plan44/p44ttngw-hardware/p44ttngw-kicad/p44ttngw.sch

## KiCad design p44ttngw-kicad/p44ttngw.sch (2017-11-21)

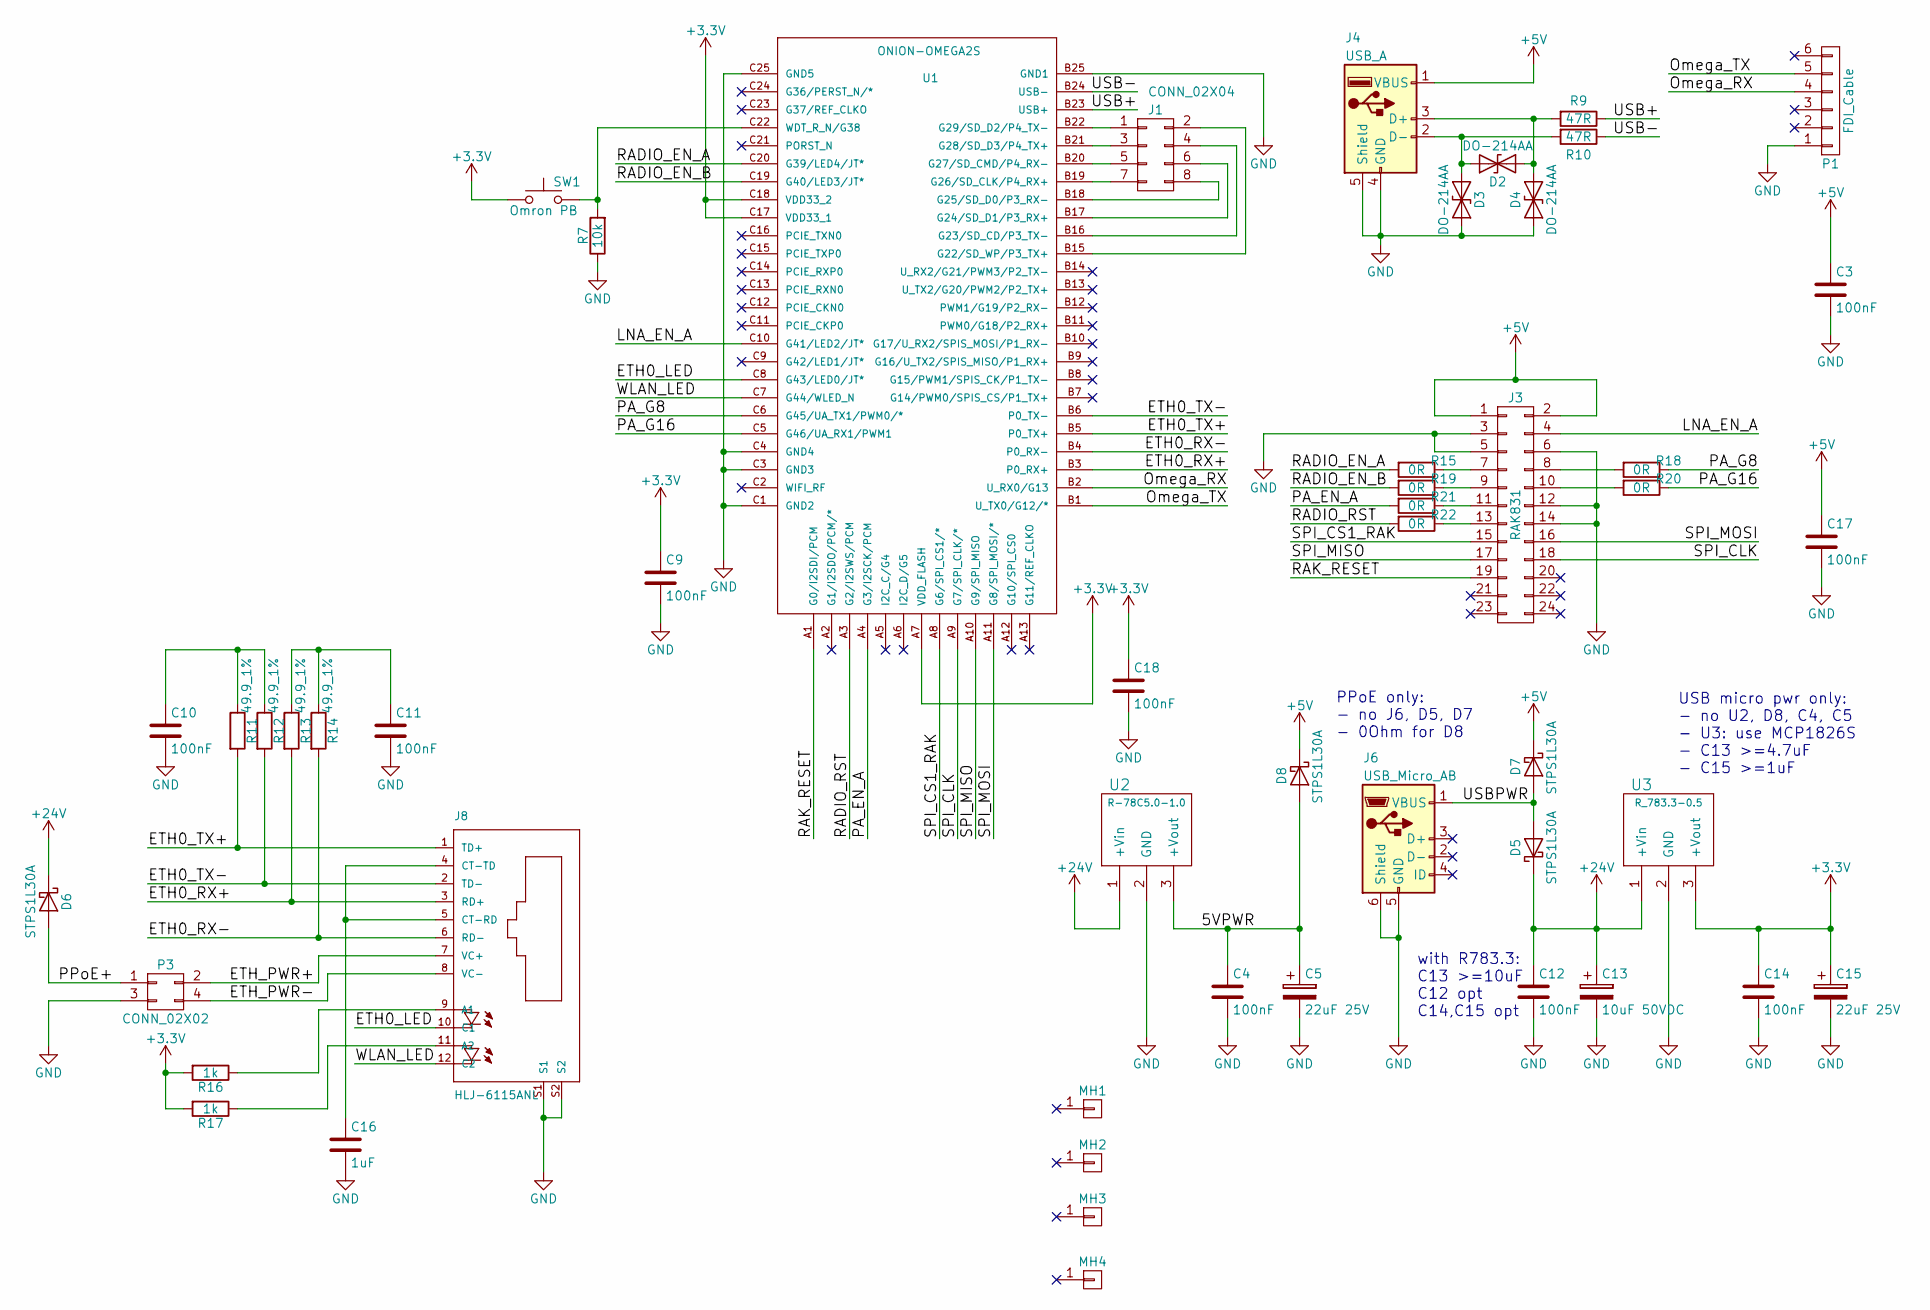
[picture p8: schematic p44ttngw.sch]

Parts:
C3, C4, C9, C10, C11, C12, C14, C17, C18: 100nF; C_1206_HandSoldering
C5, C15: 22uF 25V; CP_Radial_D7.5mm_P2.50mm
C13: 10uF 50VDC; CP_Radial_D7.5mm_P2.50mm
C16: 1uF; C_1206_HandSoldering
D2, D3, D4: DO-214AA; D_SMB_Handsoldering
D5, D6, D7, D8: STPS1L30A; D_SMA_Handsoldering
J1: CONN_02X04; Pin_Header_Straight_2x04_Pitch2.54mm
J3: RAK831
J4: USB_A
J6: USB_Micro_AB; USB_Micro-B-SMD
J8: HLJ-6115ANL
MH1, MH2, MH3, MH4: CONN_01X01; MountingHole_3.2mm_M3_DIN965_Pad
P1: FDI_Cable; Pin_Header_Straight_1x06_Pitch2.54mm
P3: CONN_02X02; Pin_Header_Straight_2x02_Pitch2.54mm
R7: 10k; R_1206_HandSoldering
R9, R10: 47R; R_1206_HandSoldering
R11, R12, R13, R14: 49.9_1%; R_0805_HandSoldering
R15, R18, R19, R20, R21, R22: 0R; R_1206_HandSoldering
R16, R17: 1k; R_1206_HandSoldering
SW1: Omron PB; SW_PUSH_6mm_h4.3mm
U1: ONION-OMEGA2S
U2: R-78C5.0-1.0; Recom-R78Cxx
U3: R_783.3-0.5; Recom-R78Cxx

Connections:
5VPWR: C4.1, C5.1, D8.2 (A), U2.3 (+Vout)
+3.3V: C9.1, C14.1, C15.1, C18.1, R16.2, R17.2, SW1.1, U1.A7 (VDD_FLASH), U1.C17 (VDD33_1), U1.C18 (VDD33_2), U3.3 (+Vout)
+5V: C3.1, C17.1, D7.1 (K), D8.1 (K), J3.1, J3.2, J4.1 (VBUS)
+24V: C12.1, C13.1, D5.1 (K), D6.1 (K), U2.1 (+Vin), U3.1 (+Vin)
ETH0_LED: J8.10 (C1), U1.C8 (G43/LED0/JT*)
ETH0_RX+: J8.3 (RD+), R13.2, U1.B3 (P0_RX+)
ETH0_RX-: J8.6 (RD-), R14.2, U1.B4 (P0_RX-)
ETH0_TX+: J8.1 (TD+), R11.2, U1.B5 (P0_TX+)
ETH0_TX-: J8.2 (TD-), R12.2, U1.B6 (P0_TX-)
ETH_PWR+: J8.7 (VC+), P3.2
ETH_PWR-: J8.8 (VC-), P3.4
GND: C3.2, C4.2, C5.2, C9.2, C10.2, C11.2, C12.2, C13.2, C14.2, C15.2, C16.2, C17.2, C18.2, D3.2 (A2), D4.2 (A2), J3.3, J3.5, J3.6, J3.12, J3.14, J4.4 (GND), J4.5 (Shield), J6.5 (GND), J6.6 (Shield), J8.S1, J8.S2, P1.1, P3.3, R7.1, U1.B25 (GND1), U1.C1 (GND2), U1.C3 (GND3), U1.C4 (GND4), U1.C25 (GND5), U2.2 (GND), U3.2 (GND)
LNA_EN_A: J3.4, U1.C10 (G41/LED2/JT*)
unnamed: C10.1, R11.1, R12.1
unnamed: C11.1, R13.1, R14.1
unnamed: C16.1, J8.4 (CT-TD), J8.5 (CT-RD)
unnamed: D2.1 (A1), D4.1 (A1), J4.3 (D+), R9.2
unnamed: D2.2 (A2), D3.1 (A1), J4.2 (D-), R10.2
unnamed: J1.1, U1.B22 (G29/SD_D2/P4_TX-)
unnamed: J1.2, U1.B15 (G22/SD_WP/P3_TX+)
unnamed: J1.3, U1.B21 (G28/SD_D3/P4_TX+)
unnamed: J1.4, U1.B16 (G23/SD_CD/P3_TX-)
unnamed: J1.5, U1.B20 (G27/SD_CMD/P4_RX-)
unnamed: J1.6, U1.B17 (G24/SD_D1/P3_RX+)
unnamed: J1.7, U1.B19 (G26/SD_CLK/P4_RX+)
unnamed: J1.8, U1.B18 (G25/SD_D0/P3_RX-)
unnamed: J3.7, R15.1
unnamed: J3.8, R18.2
unnamed: J3.9, R19.1
unnamed: J3.10, R20.2
unnamed: J3.11, R21.1
unnamed: J3.13, R22.1
unnamed: J8.9 (A1), R16.1
unnamed: J8.11 (A2), R17.1
unnamed: R7.2, SW1.2, U1.C22 (WDT_R_N/G38)
Omega_RX: P1.4, U1.B2 (U_RX0/G13)
Omega_TX: P1.5, U1.B1 (U_TX0/G12/*)
PA_EN_A: R21.2, U1.A4 (G3/I2SCK/PCM)
PA_G8: R18.1, U1.C6 (G45/UA_TX1/PWM0/*)
PA_G16: R20.1, U1.C5 (G46/UA_RX1/PWM1)
PPoE+: D6.2 (A), P3.1
RADIO_EN_A: R15.2, U1.C20 (G39/LED4/JT*)
RADIO_EN_B: R19.2, U1.C19 (G40/LED3/JT*)
RADIO_RST: R22.2, U1.A3 (G2/I2SWS/PCM)
RAK_RESET: J3.19, U1.A1 (G0/I2SDI/PCM)
SPI_CLK: J3.18, U1.A9 (G7/SPI_CLK/*)
SPI_CS1_RAK: J3.15, U1.A8 (G6/SPI_CS1/*)
SPI_MISO: J3.17, U1.A10 (G9/SPI_MISO)
SPI_MOSI: J3.16, U1.A11 (G8/SPI_MOSI/*)
USB+: R9.1, U1.B23 (USB+)
USB-: R10.1, U1.B24 (USB-)
USBPWR: D5.2 (A), D7.2 (A), J6.1 (VBUS)
WLAN_LED: J8.12 (C2), U1.C7 (G44/WLED_N)

Notes on the sheet:
USB micro pwr only: - no U2, D8, C4, C5 - U3: use MCP1826S - C13 >=4.7uF - C15 >=1uF
with R783.3: C13 >=10uF C12 opt C14,C15 opt
PPoE only: - no J6, D5, D7 - 0Ohm for D8
